juse1235/Led-merkki/kicad/kone/konekiltauusi.jpeg

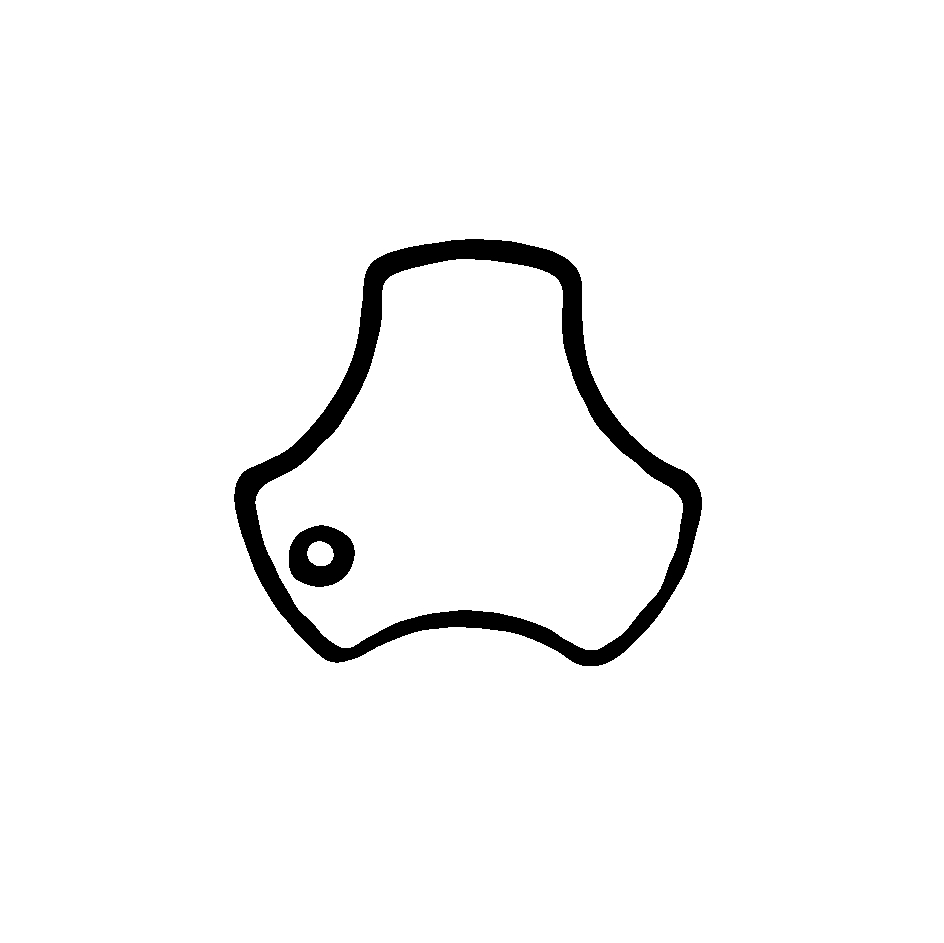
kicad/kone/konekiltauusi.jpeg
